BASLQC/xwhatits-capsense-controller/src/diag.c

/******************************************************************************
  Copyright 2014 Tom Wong-Cornall

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
  You should have received a copy of the GNU General Public License
  along with this program.  If not, see <http://www.gnu.org/licenses/>.  
 ******************************************************************************/
#include "diag.h"

#if defined (__AVR_ATmega8U2__)
void (*bootloader)(void) = (void *)0x0800;
#elif defined (__AVR_ATmega32U2__)
void (*bootloader)(void) = (void *)0x1800;
#endif

static DiagReportState diagReportState;

/*
 *
 */
static void
diagReportInfo(uint8_t *reportData, bool usingNKROReport)
{
	reportData[1] = 4; // number of layers
	reportData[2] = LAYERS_NUM_CONDITIONS;
	reportData[3] = KBD_COLS;
	reportData[4] = KBD_ROWS;

#if defined(BEAMSPRING)
	reportData[5] = dktBeamspring;
#elif defined(BEAMSPRING_DISPLAYWRITER)
	reportData[5] = dktBeamspringDisplaywriter;
#elif defined(MODEL_F)
	reportData[5] = dktModelF;
#else
#	error "keyboard type not known!"
#endif
	reportData[6] = usingNKROReport;
}

/*
 *
 */
static void
diagReportKbd(uint8_t *reportData, uint8_t startCol, uint8_t endCol)
{
	/* data is sent column-major, one column per byte (even on 4-row kbd) */
	uint8_t currByte = 1;

	for (uint8_t col = startCol; col <= endCol; col++, currByte++)
		for (uint8_t row = 0; row < KBD_ROWS; row++)
			if (scanState[col][row] >= SCAN_DB_THRESH)
				reportData[currByte] |= (1 << row);
}

/*
 *
 */
static void
diagReportVref(uint8_t *reportData)
{
	uint16_t vref = vrefGet();
	reportData[1] = vref & 0xff;
	reportData[2] = vref >> 8;
}

/*
 *
 */
static void
diagReportScanCodes(uint8_t *reportData)
{
	static uint8_t currLayer = 0;
	static uint8_t currSlice = 0;
	static uint8_t currCol = 0;

	uint8_t oldSelectedLayer = layersSelectedLayer;
	if (currLayer != layersSelectedLayer)
		layersLoad(currLayer);

	/* first byte of report has layer in top two bits, the current row slice
	 * in the next bit (we do four rows at a time), and column in the
	 * bottom 5.
	 */
	reportData[1] = (currLayer << 6) | (currSlice << 5) | currCol;

	if (KBD_ROWS == 4 || currSlice == 0)
		for (uint8_t i = 0; i < 4; i++)
			reportData[i + 2] = layersMatrix[currCol][i];
	else if (KBD_ROWS == 8 && currSlice == 1)
		for (uint8_t i = 4; i < 8; i++)
			reportData[i - 2] = layersMatrix[currCol][i];

	currCol++;
	if (currCol == KBD_COLS) {
		currCol = 0;

#if KBD_ROWS == 8
		currSlice++;
		if (currSlice == 1)
			return;
		else
			currSlice = 0;
#endif

		currLayer++;
		if (currLayer == 4)
			currLayer = 0;
	}

	if (currLayer != oldSelectedLayer)
		layersLoad(oldSelectedLayer);
}

/*
 *
 */
static void
diagReportLayerConditions(uint8_t *reportData)
{
	static uint8_t currSet = 0; // sent in two halves

	reportData[1] = currSet;

	memcpy(&reportData[2],
	       &layersConditions[currSet * (LAYERS_NUM_CONDITIONS / 2)],
	       LAYERS_NUM_CONDITIONS / 2);

	currSet++;
	if (currSet == 2)
		currSet = 0;
}

/*
 *
 */
static void
diagReportVersion(uint8_t *reportData)
{
	char *c = PSTR(VERSION);
	uint8_t i = 1;

	while ((reportData[i++] = pgm_read_byte(c++)) != '\0' && i < 7)
		;
	reportData[i] = '\0';
}

/*
 *
 */
static void
diagReportExpMode(uint8_t *reportData)
{
	reportData[1] = expMode;
	reportData[2] = expVal1;
	reportData[3] = expVal2;
}

/*
 *
 */
static void
diagReportKbdColSkips(uint8_t *reportData)
{
	memcpy(&reportData[1], kbdColSkips, sizeof(kbdColSkips));
}

/*
 *
 */
static void
diagReportEEPROM(uint8_t *reportData)
{
	static uint8_t fourByteSegment = 0;

	uint16_t addr = fourByteSegment * 4;

	reportData[1] = fourByteSegment;
	eeprom_read_block(&reportData[2], addr, 4);

	if (++fourByteSegment >= (1024 / 4))
		fourByteSegment = 0;
}

/*
 *
 */
static void
diagReportDebug(uint8_t *reportData)
{
	//static uint8_t index = 0;

	//reportData[1] = index;
	//reportData[2] = kbdPrevSCBmp[index];

	//index++;
	//if (index >= sizeof(kbdPrevSCBmp))
	//    index = 0;

	reportData[1] = 0;
	reportData[2] = scanTick;
}

/*
 *
 */
static void
diagReportMacroEEPROMSize(uint8_t *reportData)
{
	uint16_t size = EEP_MACROS_BND - EEP_MACROS;
	reportData[1] =  size & 0xff;
	reportData[2] = (size >> 8);
}

/*
 *
 */
static void
diagReportMacros(uint8_t *reportData)
{
	static uint8_t fourByteSegment = 0;

	uint8_t *addr = (uint8_t *)(fourByteSegment * 4 + EEP_MACROS);

	reportData[1] = fourByteSegment;
	for (uint8_t i = 0; i < 4; i++) {
		if ((uint16_t)addr >= EEP_MACROS_BND)
			break;
		reportData[2 + i] = eeprom_read_byte(addr++);
	}

	if (++fourByteSegment >= ((EEP_MACROS_BND - EEP_MACROS) / 4))
		fourByteSegment = 0;
}

/*
 *
 */
static void
diagSetScanCode(uint8_t layer, uint8_t col, uint8_t row, uint8_t sc)
{
	if (layer >= 0 && layer < 4 &&
	    col >= 0 && col < KBD_COLS &&
	    row >= 0 && row < KBD_ROWS)
		layersSetScancode(layer, col, row, sc);
}

/*
 *
 */
static void
diagSetLayerCondition(uint8_t conditionIdx, uint8_t val)
{
	if (conditionIdx >= 0 && conditionIdx < LAYERS_NUM_CONDITIONS)
		layersSetCondition(conditionIdx, val);
}

/*
 *
 */
static void
diagSetExpMode(uint8_t mode, uint8_t val1, uint8_t val2)
{
	expMode = mode;
	expVal1 = val1;
	expVal2 = val2;

	expReset();
}

/*
 *
 */
static void
diagSetKbdColSkips(const uint8_t *reportData)
{
	memcpy(kbdColSkips, &reportData[1], sizeof(kbdColSkips));
}

/*
 *
 */
static void
diagWriteEEPROMByte(uint8_t *addr, uint8_t val)
{
	if ((uint16_t)addr >= 1024)
		return;
	eeprom_update_byte(addr, val);
}

/*
 *
 */
static void
writeMacroByte(uint8_t *addr, uint8_t val)
{
	if (addr <  (uint8_t *)EEP_MACROS ||
	    addr >= (uint8_t *)EEP_MACROS_BND)
		return;

	eeprom_update_byte(addr, val);
}

/*
 *
 */
static void
diagWriteMacroSegment(uint8_t fourByteSegment,
		      uint8_t byte1,
		      uint8_t byte2,
		      uint8_t byte3,
		      uint8_t byte4)
{
	uint8_t *addr = (uint8_t *)(fourByteSegment * 4 + EEP_MACROS);
	writeMacroByte(addr++, byte1);
	writeMacroByte(addr++, byte2);
	writeMacroByte(addr++, byte3);
	writeMacroByte(addr,   byte4);
}

/*
 *
 */
void
diagReceiveReport(const uint8_t *reportData)
{
	DiagReportCommand cmd = reportData[0];

	switch (cmd) {
	case dcSetState:
		diagReportState = reportData[1];
		break;
	case dcSetVref:
		vrefSet(reportData[1] + (reportData[2] << 8));
		break;
	case dcJumpBootloader:
		if (reportData[1]) {
			scanDisable(); // otherwise IRQ will wreak havoc
			bootloader();
		}
		break;
	case dcStoreVref:
		if (reportData[1])
			vrefStore();
		break;
	case dcAutoCalibrate:
		if (reportData[1])
			kbdCalibrate();
		break;
	case dcSetScanCode:
		diagSetScanCode(reportData[1] >> 6, reportData[1] & 0x3f,
				reportData[2], reportData[3]);
		break;
	case dcSetLayerCondition:
		diagSetLayerCondition(reportData[1], reportData[2]);
		break;
	case dcSetExpMode:
		diagSetExpMode(reportData[1], reportData[2], reportData[3]);
		break;
	case dcStoreExpMode:
		if (reportData[1])
			expStore();
		break;
	case dcSetKbdColSkips:
		diagSetKbdColSkips(reportData);
		break;
	case dcStoreKbdColSkips:
		if (reportData[1])
			kbdStoreColSkips();
		break;
	case dcWriteEEPROMByte:
		diagWriteEEPROMByte(reportData[1] +
				    (uint8_t *)(reportData[2] << 8),
				    reportData[3]);
		break;
	case dcSetScanEnabled:
		if (reportData[1])
			scanEnable();
		else
			scanDisable();
		break;
	case dcWriteMacroSegment:
		diagWriteMacroSegment(reportData[1],
				      reportData[2],
				      reportData[3],
				      reportData[4],
				      reportData[5]);
		break;
	case dcLoadMacros:
		if (reportData[1])
			macrosInit();
	default:
		break;
	}
}

/*
 *
 */
void
diagFillReport(uint8_t *reportData, bool usingNKROReport)
{
	/* zero report */
	memset(reportData, 0x00, GENERIC_REPORT_SIZE);

	/* first byte of report is reporting state */
	reportData[0] = diagReportState;

	switch (diagReportState) {
	case drInfo:
		diagReportInfo(reportData, usingNKROReport);
		diagReportState = drNothing;
		break;
	case dr1stCols:
		diagReportKbd(reportData, 0, 6);
		diagReportState = dr2ndCols;
		break;
	case dr2ndCols:
#if KBD_COLS == 12
		diagReportKbd(reportData, 7, 11);
#elif KBD_COLS == 16 || KBD_COLS == 23
		diagReportKbd(reportData, 7, 13);
#endif
		diagReportState = dr3rdCols;
		break;
	case dr3rdCols:
#if KBD_COLS == 12
		diagReportState = drNothing;
#elif KBD_COLS == 16
		diagReportKbd(reportData, 14, 15);
		diagReportState = drNothing;
#elif KBD_COLS == 23
		diagReportKbd(reportData, 14, 20);
		diagReportState = dr4thCols;
#else
#	error "kbd columns not 12, 16 or 23"
#endif
		break;
	case dr4thCols:
#if KBD_COLS == 12 || KBD_COLS == 16
#elif KBD_COLS == 23
		diagReportKbd(reportData, 21, 23);
#else
#	error "kbd columns not 16 or 23"
#endif
		diagReportState = drNothing;
		break;
	case drVref:
		diagReportVref(reportData);
		diagReportState = drNothing;
		break;
	case drScanCodes:
		diagReportScanCodes(reportData);
		break;
	case drLayerConditions:
		diagReportLayerConditions(reportData);
		break;
	case drVersion:
		diagReportVersion(reportData);
		diagReportState = drNothing;
		break;
	case drExpMode:
		diagReportExpMode(reportData);
		diagReportState = drNothing;
		break;
	case drKbdColSkips:
		diagReportKbdColSkips(reportData);
		diagReportState = drNothing;
		break;
	case drEEPROM:
		diagReportEEPROM(reportData);
		break;
	case drDebug:
		diagReportDebug(reportData);
		break;
	case drMacroEEPROMSize:
		diagReportMacroEEPROMSize(reportData);
		break;
	case drMacros:
		diagReportMacros(reportData);
		break;
	default:
		break;
	}
}
