BASLQC/xwhatits-capsense-controller/src/layers.c

/******************************************************************************
  Copyright 2014 Tom Wong-Cornall

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
  You should have received a copy of the GNU General Public License
  along with this program.  If not, see <http://www.gnu.org/licenses/>.  
 ******************************************************************************/
#include "layers.h"

uint8_t layersMatrix[KBD_COLS][KBD_ROWS];
uint8_t layersConditions[LAYERS_NUM_CONDITIONS];
uint8_t layersDefaultLayer;
uint8_t layersSelectedLayer;

static void     layersLoadConditions(void);
static uint8_t *layersEEPAddr(uint8_t layer);

/*
 *
 */
void
layersInit(void)
{
	layersDefaultLayer = 0;
	layersLoad(0);
	layersLoadConditions();
}

/*
 *
 */
uint8_t *
layersEEPAddr(uint8_t layer)
{
	switch (layer) {
	case 0: return (uint8_t *)EEP_LAYER_MATRIX_0;
	case 1: return (uint8_t *)EEP_LAYER_MATRIX_1;
	case 2: return (uint8_t *)EEP_LAYER_MATRIX_2;
	case 3: return (uint8_t *)EEP_LAYER_MATRIX_3;
	}

	return (uint8_t *)EEP_LAYER_MATRIX_0;
}

/*
 *
 */
void
layersLoad(uint8_t layer)
{
	const uint8_t *addr = layersEEPAddr(layer);

	for (uint8_t col = 0; col < KBD_COLS; col++) {
		for (uint8_t row = 0; row < KBD_ROWS; row++) {
			uint8_t sc = eeprom_read_byte(addr++);
			if (sc == 0xff)
				sc = KBD_SC_IGNORED;
			layersMatrix[col][row] = sc;
		}
	}

	layersSelectedLayer = layer;
}

/*
 *
 */
void
layersSetScancode(uint8_t layer, uint8_t col, uint8_t row, uint8_t sc)
{
	uint8_t *addr = layersEEPAddr(layer);

	if (layer == layersSelectedLayer)
		layersMatrix[col][row] = sc;

	addr += (col * KBD_ROWS) + row;

	eeprom_update_byte(addr, sc);
}

/*
 *
 */
void
layersLoadConditions(void)
{
	eeprom_read_block(layersConditions,
			  (const void *)EEP_LAYER_CNDS,
			  sizeof(layersConditions));
}

/*
 *
 */
void
layersStoreConditions(void)
{
	eeprom_update_block(layersConditions,
			    (void *)EEP_LAYER_CNDS,
			    sizeof(layersConditions));
}

/*
 *
 */
void
layersSetCondition(uint8_t idx, uint8_t val)
{
	layersConditions[idx] = val;
	eeprom_update_byte((uint8_t *)EEP_LAYER_CNDS + idx, val);
}

/*
 * check for Fn or Select keys in order to switch layer
 */
void
layersProcessScan(void)
{
	/* first look for select keycodes to change default layer; use key-up
	 * to trigger switch, making it possible to use the same key to toggle
	 * between layers.
	 */
	if ( kbdSCIsIn(KBD_SC_SELECT_0, kbdPrevSCBmp) &&
	    !kbdSCIsIn(KBD_SC_SELECT_0, kbdSCBmp))
		layersDefaultLayer = 0;
	else if ( kbdSCIsIn(KBD_SC_SELECT_1, kbdPrevSCBmp) &&
		 !kbdSCIsIn(KBD_SC_SELECT_1, kbdSCBmp))
		layersDefaultLayer = 1;
	else if ( kbdSCIsIn(KBD_SC_SELECT_2, kbdPrevSCBmp) &&
		 !kbdSCIsIn(KBD_SC_SELECT_2, kbdSCBmp))
		layersDefaultLayer = 2;
	else if ( kbdSCIsIn(KBD_SC_SELECT_3, kbdPrevSCBmp) &&
		 !kbdSCIsIn(KBD_SC_SELECT_3, kbdSCBmp))
		layersDefaultLayer = 3;

	uint8_t result = layersDefaultLayer;

	/* we can rely on fn keys scancodes being byte-aligned, but we only
	 * want the lower three bits
	 */
	uint8_t fnKeys = (kbdSCBmp[KBD_SC_FN1 / 8] & 0x7);
	if (fnKeys != 0) {
		/* condition is in high nibble, resulting layer is in low */
		for (uint8_t i = 0; i < LAYERS_NUM_CONDITIONS; i++)
			if (layersConditions[i] >> 4 == fnKeys)
				result = layersConditions[i] & 0xf;
	}

	if (result != layersSelectedLayer)
		layersLoad(result);
}
