BASLQC/xwhatits-capsense-controller/src/sr.h

/******************************************************************************
  Copyright 2014 Tom Wong-Cornall

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
  You should have received a copy of the GNU General Public License
  along with this program.  If not, see <http://www.gnu.org/licenses/>.  
 ******************************************************************************/
#ifndef SR_H
#define SR_H

#include <avr/io.h>

/* row drive shift registers */

/* pin definitions */
#if defined(BEAMSPRING)
#       define SR_DDR   DDRC
#       define SR_PORT  PORTC
#       define SR_D_OP  PC4
#       define SR_C_OP  PC5
#       define SR_OE_OP PC6
#	if BOARD_REV == 4
#               define SR_STCP_OP PC7
#       endif
#elif defined(BEAMSPRING_DISPLAYWRITER) || defined(MODEL_F)
#       define SR_DDR     DDRD
#	define SR_PORT    PORTD
#	define SR_D_OP    PD4
#	define SR_C_OP    PD7
#	define SR_OE_OP   PD5
#	define SR_STCP_OP PD6
#endif

/* shift register specifics */
#if defined(BEAMSPRING) && BOARD_REV <= 3
/* 	4094 shift registers have active-high OE */
#	define srEnable()  (SR_PORT |=  (1 << SR_OE_OP))
#	define srDisable() (SR_PORT &= ~(1 << SR_OE_OP))
#elif defined(BEAMSPRING_DISPLAYWRITER) || defined(MODEL_F)  || \
   (defined(BEAMSPRING) && BOARD_REV == 4)
/* 	595 shift registers have active-low OE, but we use the strobe instead */
#	define srEnable()           \
   do {                             \
	   SR_PORT |=  (1 << SR_STCP_OP);  \
	   SR_PORT &= ~(1 << SR_STCP_OP);  \
   } while (0)                           
#	define srDisable()     /* nothing */
#else
#	error "BOARD_TYPE not specified in makefile"
#endif

void	srInit(void);

/* these defined as macros, as will be used inline in scan interrupt */
#define srClear()                                       \
   do {                                                 \
	   for (uint8_t i = 0; i < KBD_COLS + 1; i++) { \
		   SR_PORT |=  (1 << SR_C_OP);          \
		   SR_PORT &= ~(1 << SR_C_OP);          \
	   }                                            \
   } while (0)

#define srSet(pos)                             \
   do {                                        \
	   SR_PORT |=  (1 << SR_D_OP);         \
	   SR_PORT |=  (1 << SR_C_OP);         \
	   SR_PORT &= ~(1 << SR_C_OP);         \
	   SR_PORT &= ~(1 << SR_D_OP);         \
	   for (uint8_t i = 0; i < pos; i++) { \
		   SR_PORT |=  (1 << SR_C_OP); \
		   SR_PORT &= ~(1 << SR_C_OP); \
	   }                                   \
   } while (0)

#endif
